DaveMcEwan/mcdox/pcb/ctrl/img/ctrl_bottom.png

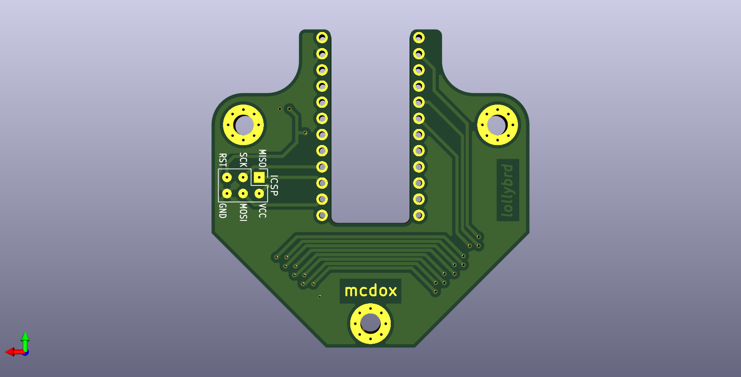
pcb/ctrl/img/ctrl_bottom.png
