DaveMcEwan/mcdox/pcb/ctrl/img/ctrl_top.png

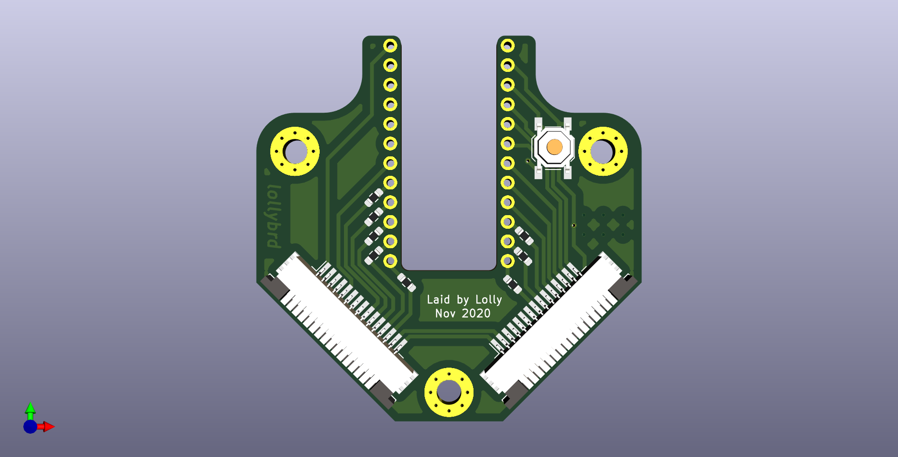
pcb/ctrl/img/ctrl_top.png
