DaveMcEwan/mcdox/pcb/hand/img/hand_bottom.png

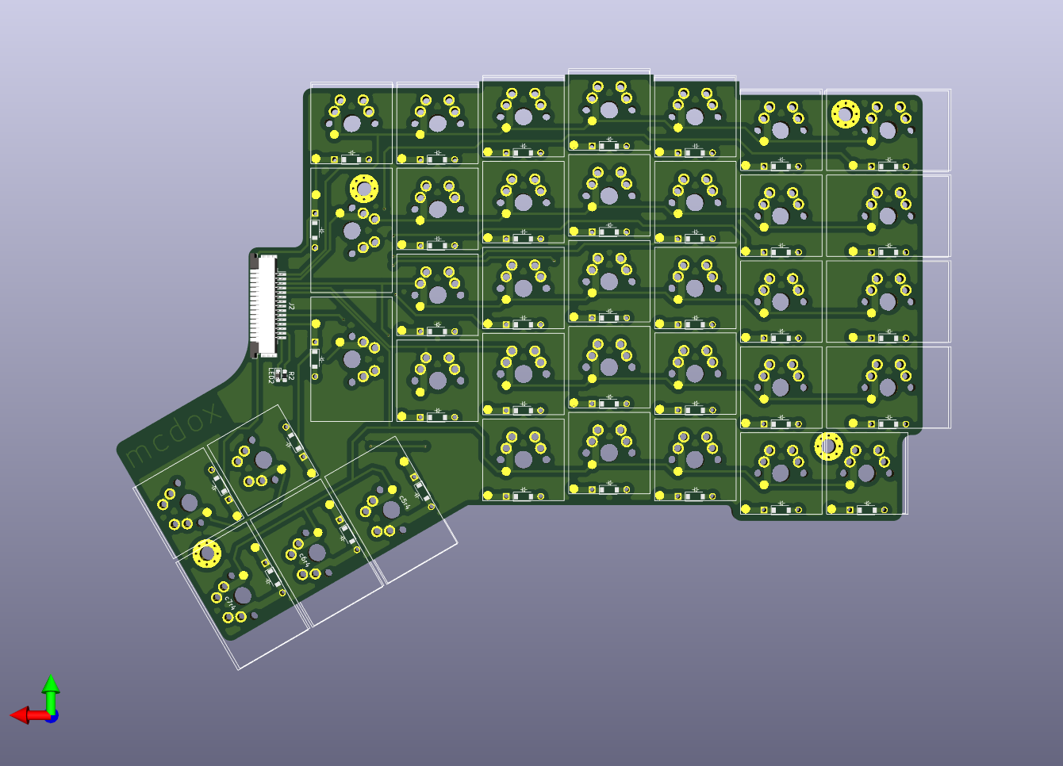
pcb/hand/img/hand_bottom.png
