DaveMcEwan/mcdox/pcb/hand/img/hand_top.png

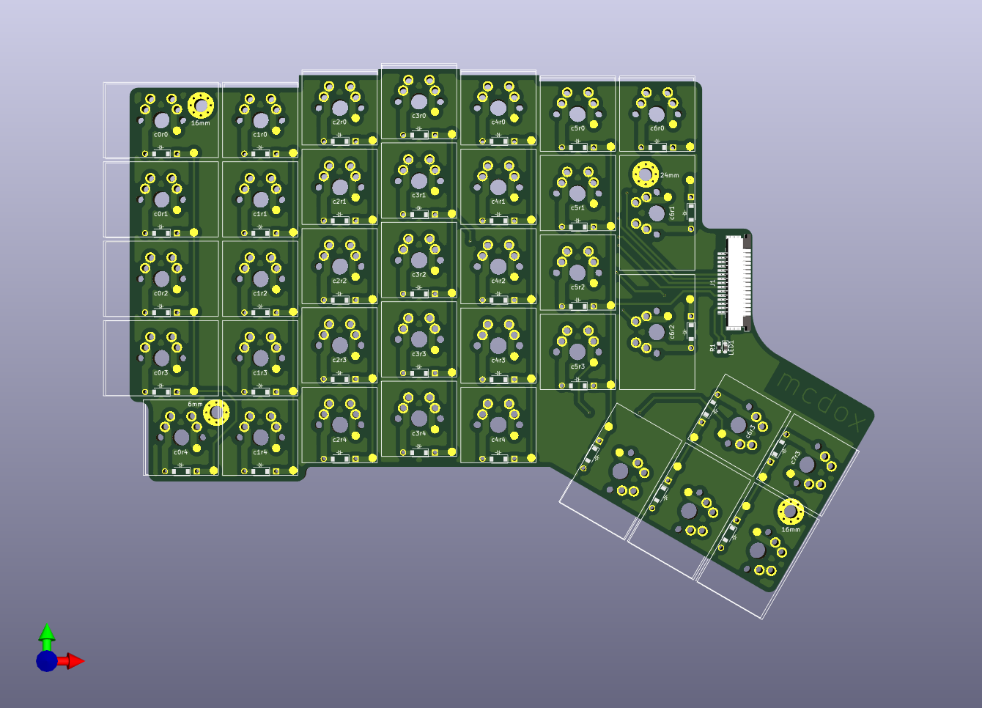
pcb/hand/img/hand_top.png
