DaveMcEwan/mcdox/release/mcdoxNov2020/img/bottom1.jpg

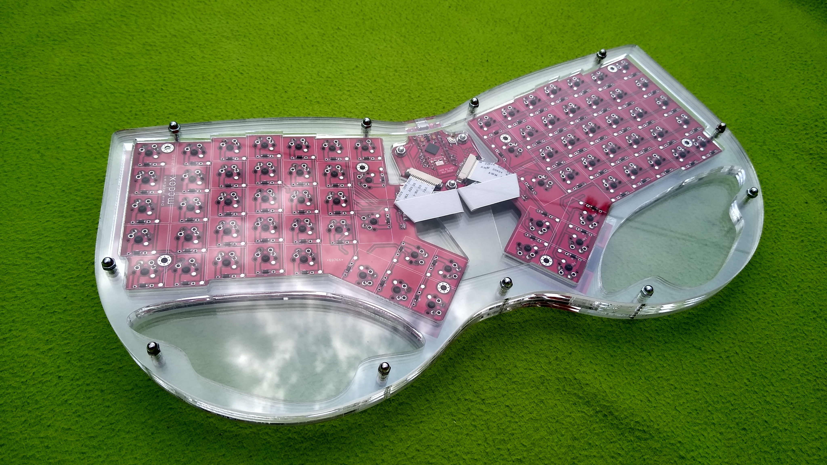
release/mcdoxNov2020/img/bottom1.jpg
