DaveMcEwan/mcdox/release/mcdoxNov2020/img/bottom2.jpg

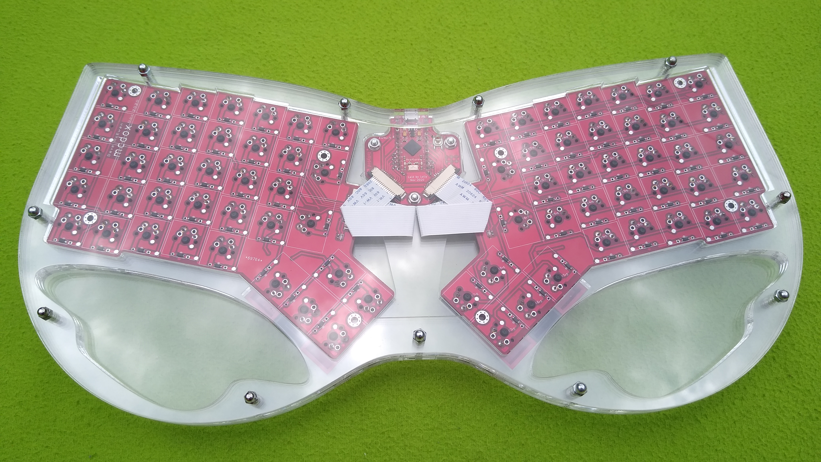
release/mcdoxNov2020/img/bottom2.jpg
