DaveMcEwan/mcdox/release/mcdoxNov2020/img/bottom3.jpg

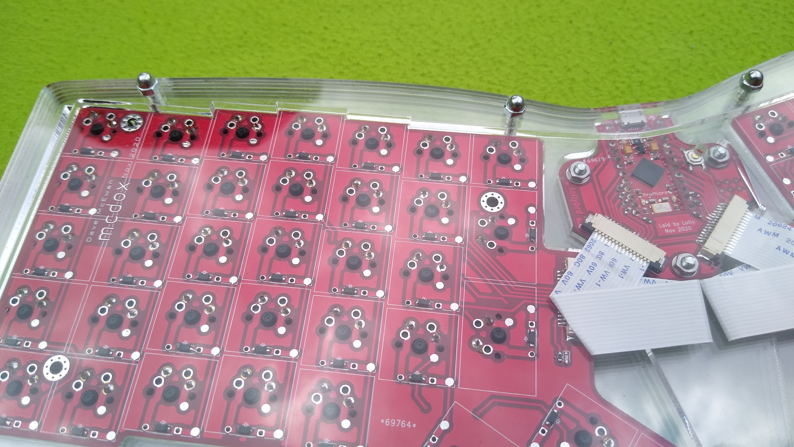
release/mcdoxNov2020/img/bottom3.jpg
