DaveMcEwan/mcdox/release/mcdoxNov2020/img/ctrl0.jpg

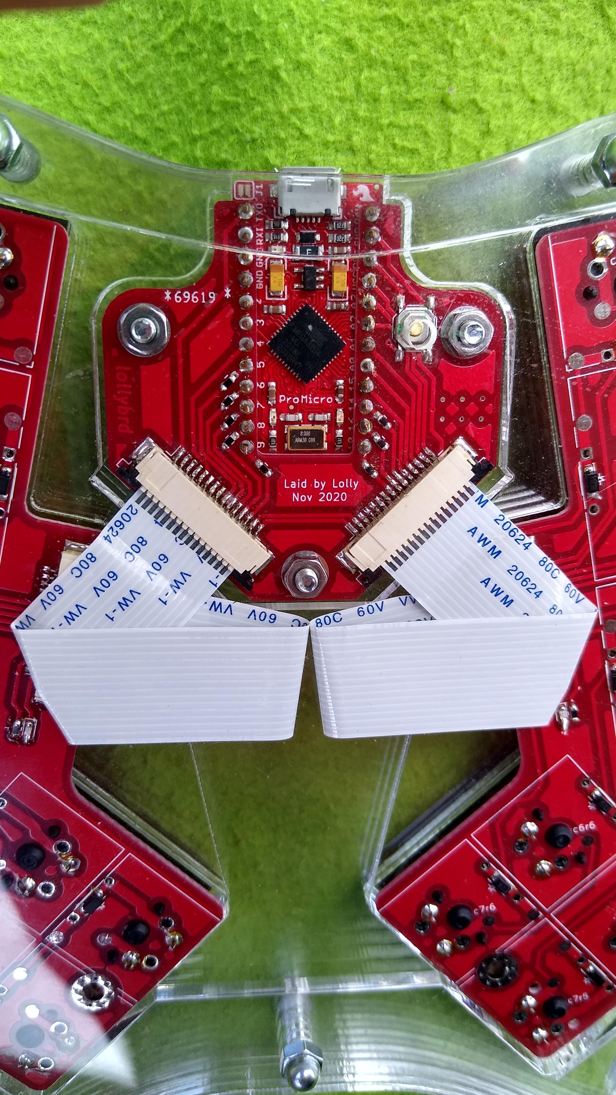
release/mcdoxNov2020/img/ctrl0.jpg
