DaveMcEwan/mcdox/release/mcdoxNov2020/img/ctrl2.jpg

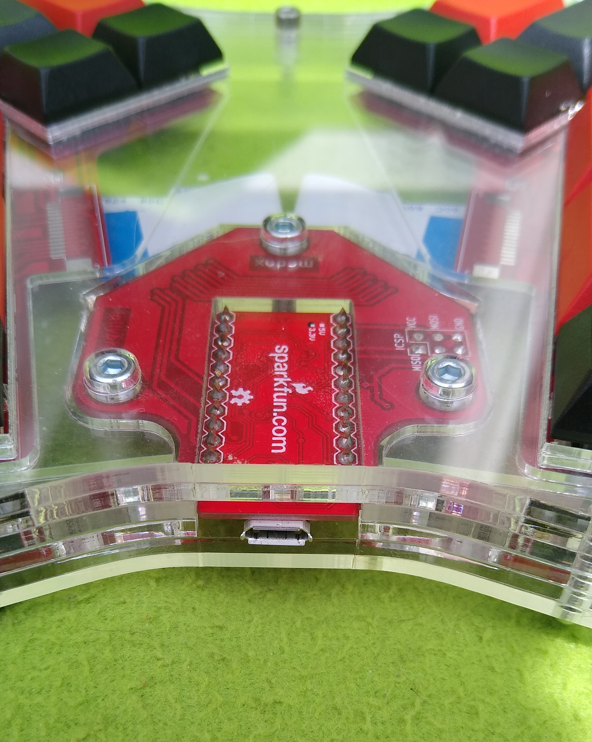
release/mcdoxNov2020/img/ctrl2.jpg
