DaveMcEwan/mcdox/release/mcdoxNov2020/img/pcbs1.jpg

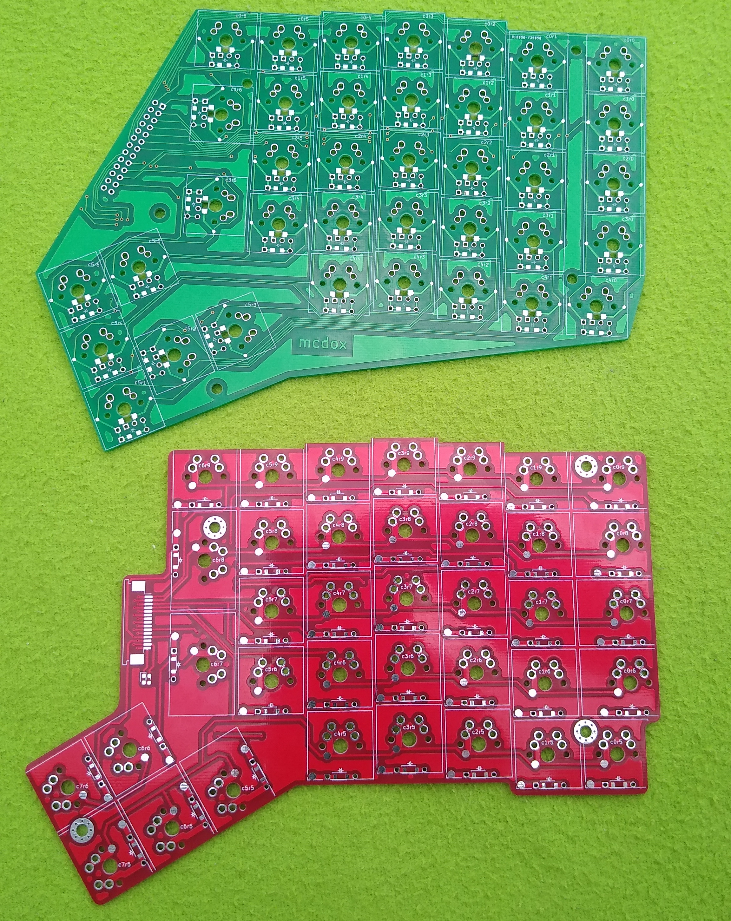
release/mcdoxNov2020/img/pcbs1.jpg
