DaveMcEwan/mcdox/release/mcdoxNov2020/img/top2.jpg

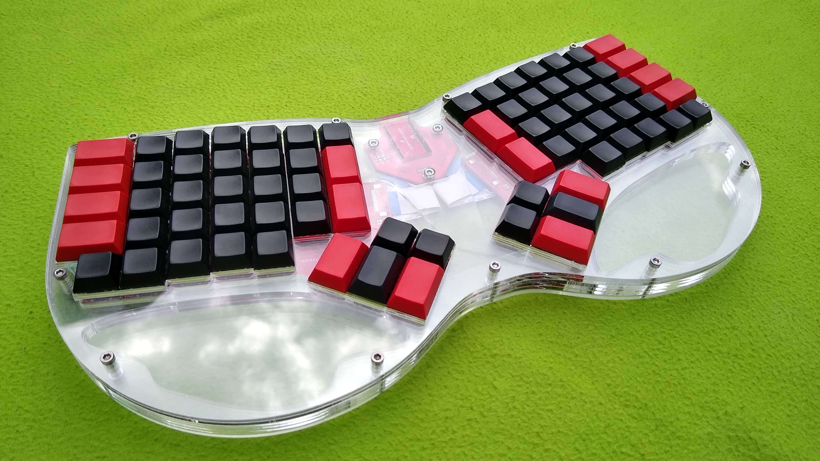
release/mcdoxNov2020/img/top2.jpg
