DaveMcEwan/mcdox/case/release/unmade_mcdoxCase/cut.coverTop.dxf

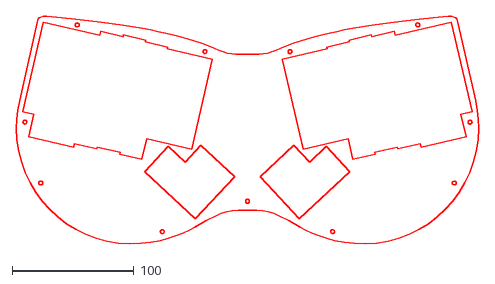
[picture p35: CAD file, 2020-12-03]
case/release/unmade_mcdoxCase/cut.coverTop.dxf
380.0 x 186.8
