DaveMcEwan/mcdox/keycap/stl/moldUpper,keycap,DSA,CherryMX,1u,noBump.stl

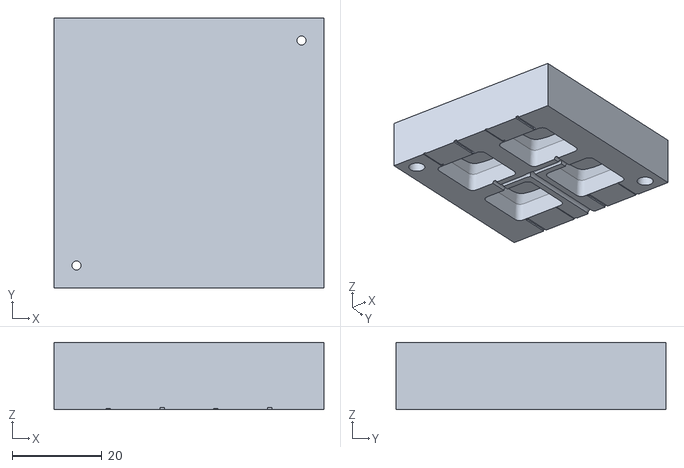
[picture p36: CAD file, 2021-05-29]
keycap/stl/moldUpper,keycap,DSA,CherryMX,1u,noBump.stl
60.0 x 60.0 x 15.0
