DaveMcEwan/mcdox/case/release/2020-12-03_MVB1.06_mcdoxCase/cut.coverBottom.dxf

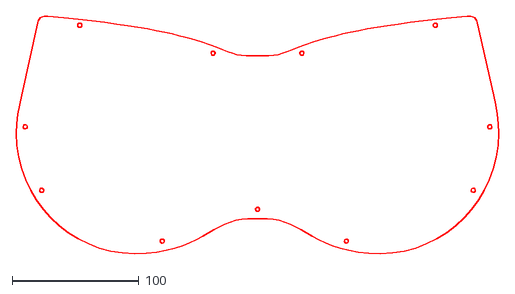
[picture p37: CAD file, 2020-12-03]
case/release/2020-12-03_MVB1.06_mcdoxCase/cut.coverBottom.dxf
380.0 x 186.9
