DaveMcEwan/mcdox/case/release/unmade_mcdoxCase/cut.mount.dxf

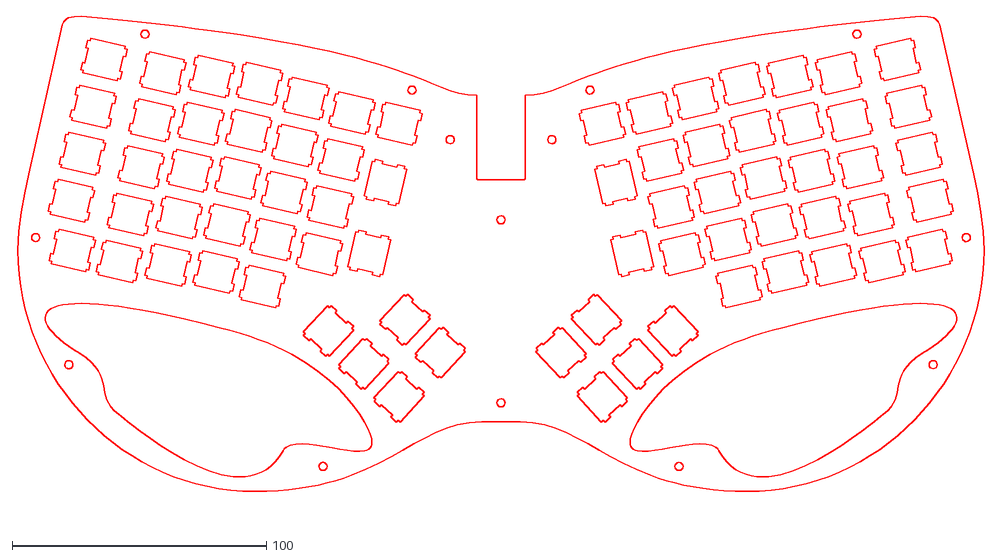
[picture p38: CAD file, 2020-12-03]
case/release/unmade_mcdoxCase/cut.mount.dxf
381.5 x 197.5
