DaveMcEwan/mcdox/case/release/2020-12-03_MVB1.06_mcdoxCase/cut.innerBottom0.dxf

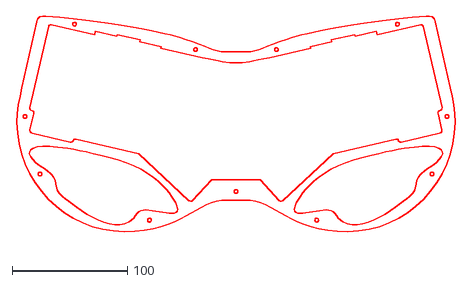
[picture p39: CAD file, 2020-12-03]
case/release/2020-12-03_MVB1.06_mcdoxCase/cut.innerBottom0.dxf
381.5 x 197.5
