DaveMcEwan/mcdox/case/release/unmade_mcdoxCase/cut.innerBottom0.dxf

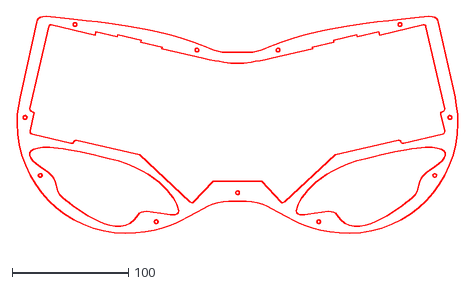
[picture p40: CAD file, 2020-12-03]
case/release/unmade_mcdoxCase/cut.innerBottom0.dxf
381.5 x 197.5
