DaveMcEwan/mcdox/lollybrd/ctrl_teensy.sch

## KiCad design lollybrd/ctrl_teensy.sch (2014-12-23)

Schematic: ctrl_teensy.sch

Parts:
P1, P4: CONN_01X02; Pin_Header_Straight_1x02
P2, P3: CONN_01X13; Pin_Header_Straight_1x13
R_left1: 220R; Resistor_Horizontal_RM15mm
R_right1: 220R; Resistor_Horizontal_RM15mm
U1: teensy; teensy_2.0
